alihatamitajik/saat-royal/code/SaRoyAl/RTC.ino

// Library forReal Time Clock Module
#include <RTClib.h>
RTC_DS1307 rtc;

bool isAlarm() {
  updateTime();
  return Prefrences.alarmH == noww.hour() &&
         Prefrences.alarmM == noww.minute() &&
         noww.second() < 5;
}

void handleAlarm() {
  if (isAlarm()) {
    Serial.println("Playing Song");
    showAlarmClock(Prefrences.alarmH, Prefrences.alarmM);
    playmelodyMario();
    turnOff();
    isOperating = false;
  }
}

void updateTime() {
  noww = rtc.now();
}

void adjustClock(uint8_t YYYY,uint8_t MM,uint8_t DD,
                 uint8_t hh,uint8_t mm,uint8_t ss){
  rtc.adjust(DateTime(YYYY, MM, DD, hh, mm, ss));
}

void initRTC(){
  if (! rtc.begin()) {
    Serial.println("Couldn't find RTC");
    Serial.flush();
    while (1) delay(10);
  }
  if (! rtc.isrunning()) {
    Serial.println("RTC is NOT running, let's set the time!");
    // When time needs to be set on a new device, or after a power loss, the
    // following line sets the RTC to the date & time this sketch was compiled
    rtc.adjust(DateTime(F(__DATE__), F(__TIME__)));
    // This line sets the RTC with an explicit date & time, for example to set
    // January 21, 2014 at 3am you would call:
    // rtc.adjust(DateTime(2014, 1, 21, 3, 0, 0));
  }
}
